Len42/dat-ting/firmware/inc/oled_fonts2.h

#pragma once

namespace daisy2 {

namespace Font {

/// @brief Dina font, converted for use with libDaisy
/// @details Dina font (c) 2005-2013 Joergen Ibsen - see LICENSE
const uint16_t Dina_r400_10_data[] = {
    /*   */ 0x0000, 0x0000, 0x0000, 0x0000, 0x0000, 0x0000, 0x0000, 0x0000, 0x0000, 0x0000, 0x0000, 0x0000, 0x0000, 0x0000, 0x0000, 0x0000, 
    /* ! */ 0x0000, 0x0000, 0x1000, 0x1000, 0x1000, 0x1000, 0x1000, 0x1000, 0x0000, 0x0000, 0x1000, 0x1000, 0x0000, 0x0000, 0x0000, 0x0000, 
    /* " */ 0x0000, 0x2400, 0x2400, 0x2400, 0x0000, 0x0000, 0x0000, 0x0000, 0x0000, 0x0000, 0x0000, 0x0000, 0x0000, 0x0000, 0x0000, 0x0000, 
    /* # */ 0x0000, 0x0000, 0x0000, 0x0000, 0x2400, 0x2400, 0x7E00, 0x2400, 0x2400, 0x7E00, 0x2400, 0x2400, 0x0000, 0x0000, 0x0000, 0x0000, 
    /* $ */ 0x0000, 0x0000, 0x1000, 0x3800, 0x5400, 0x5000, 0x5000, 0x3800, 0x1400, 0x1400, 0x5400, 0x3800, 0x1000, 0x0000, 0x0000, 0x0000, 
    /* % */ 0x0000, 0x0000, 0x0000, 0x6000, 0x9200, 0x9400, 0x6800, 0x1000, 0x2C00, 0x5200, 0x9200, 0x0C00, 0x0000, 0x0000, 0x0000, 0x0000, 
    /* & */ 0x0000, 0x0000, 0x1800, 0x2400, 0x2400, 0x2800, 0x1000, 0x2A00, 0x4400, 0x4400, 0x4400, 0x3A00, 0x0000, 0x0000, 0x0000, 0x0000, 
    /* ' */ 0x0000, 0x1000, 0x1000, 0x1000, 0x0000, 0x0000, 0x0000, 0x0000, 0x0000, 0x0000, 0x0000, 0x0000, 0x0000, 0x0000, 0x0000, 0x0000, 
    /* ( */ 0x0000, 0x0800, 0x1000, 0x1000, 0x2000, 0x2000, 0x2000, 0x2000, 0x2000, 0x2000, 0x2000, 0x1000, 0x1000, 0x0800, 0x0000, 0x0000, 
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
    /* F */ 0x0000, 0x0000, 0x0000, 0x7E00, 0x4000, 0x4000, 0x4000, 0x7C00, 0x4000, 0x4000, 0x4000, 0x4000, 0x0000, 0x0000, 0x0000, 0x0000, 
    /* G */ 0x0000, 0x0000, 0x0000, 0x3C00, 0x4200, 0x4000, 0x4000, 0x4E00, 0x4200, 0x4200, 0x4200, 0x3C00, 0x0000, 0x0000, 0x0000, 0x0000, 
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
};
FontDef Dina_r400_10 = { 8, 16, Dina_r400_10_data };

}

}
