Len42/dat-ting/firmware/inc/tasks.h

#pragma once

/// @brief A simple, efficient task scheduler for embedded microcontrollers
///
/// This task scheduler is designed to be simple to use and to have very little
/// overhead in time and memory. Some compile-time tricks are used to create a
/// static list of tasks, while keeping the application-level code simple with
/// a minimum of boilerplate.
/// 
/// Usage
/// -----
/// To define a set of tasks:
/// 
/// 1. Define each task as a subclass of Tasks::Task like this.
/// A single instance of this class will be created automatically.
/// @code
/// class ExampleTask : public Tasks::Task
/// {
/// public:
///     // Task execution interval in microseconds
///     unsigned intervalMicros() const { return 1'000'000; }
/// 
///     // Task initialization, called once at program start
///     void init()
///     {
///         // task initialization code
///     }
/// 
///     // Main task function, executed at (approximately) the specified interval
///     void execute()
///     {
///         // task main code
///     }
/// };
/// @endcode
/// 2. Make a list of all the tasks by declaring a specialization of Tasks::TaskList.
/// Any tasks not currently required (e.g. for debugging) can be commented out
/// and the unused task code will not be compiled into the executable.
/// @code
/// using TaskList = Tasks::TaskList<
///     ExampleTask,
///     AnotherTask,
///     AndAnotherTask
/// >;
/// @endcode
/// 3. In main(), initialize all the tasks and then execute them repeatedly.
/// @code
/// int main()
/// {
///     // Initialize all the tasks.
///     TaskList::initAll();
///
///     // Execute all the tasks repeatedly, at their specified time intervals.
///     while (true) {
///         TaskList::runAll();
///     }
///
///     return 0;
/// }
/// @endcode

#include "daisy_seed2.h" // system dependencies

namespace tasks {

using tasktime_t = daisy2::System2::timeus_t; // elapsed time, in microseconds

/// @brief Return elapsed time since startup, in microseconds (approximately)
/// @return Microseconds since startup
inline tasktime_t getCurrentMicros()
{
    return daisy2::System2::GetUsLong();
}

/// @brief  Base class for application-defined tasks
class Task
{
public:
    /// @brief If it's time to call execute(), do so
    /// @param self "this" object with deduced subclass type
    /// @param now Current time
    void tick(this auto&& self, tasktime_t now)
    {
        if (now >= self.timer) {
            self.timer = getCurrentMicros() + self.intervalMicros();
            self.execute();
        }
    }

private:
    /// @brief Keeps track of the next time this task should be executed
    tasktime_t timer = 0;
};

/// @brief A static list of Task that is initialized at compile time
/// @tparam ...TASKS List of Task subclasses
template<typename... TASKS>
class TaskList
{
public:
    /// @brief Initialize all the tasks
    static void initAll()
    {
        ((taskInstance<TASKS>.init()), ...);
    }

    /// @brief Execute all the tasks repeatedly, at their specified time intervals
    static void runAll()
    {
        tasktime_t now = getCurrentMicros();
        ((taskInstance<TASKS>.tick(now)), ...);
    }

protected:
    /// @brief There is one static instance of each subclass of Task
    /// @tparam TASK_T A subclass of Task
    template<typename TASK_T>
    static inline TASK_T taskInstance;
};

} // namespace tasks
